WingTechCorner/I2C_Multiplexer/images/I2C-MuxBoard.png

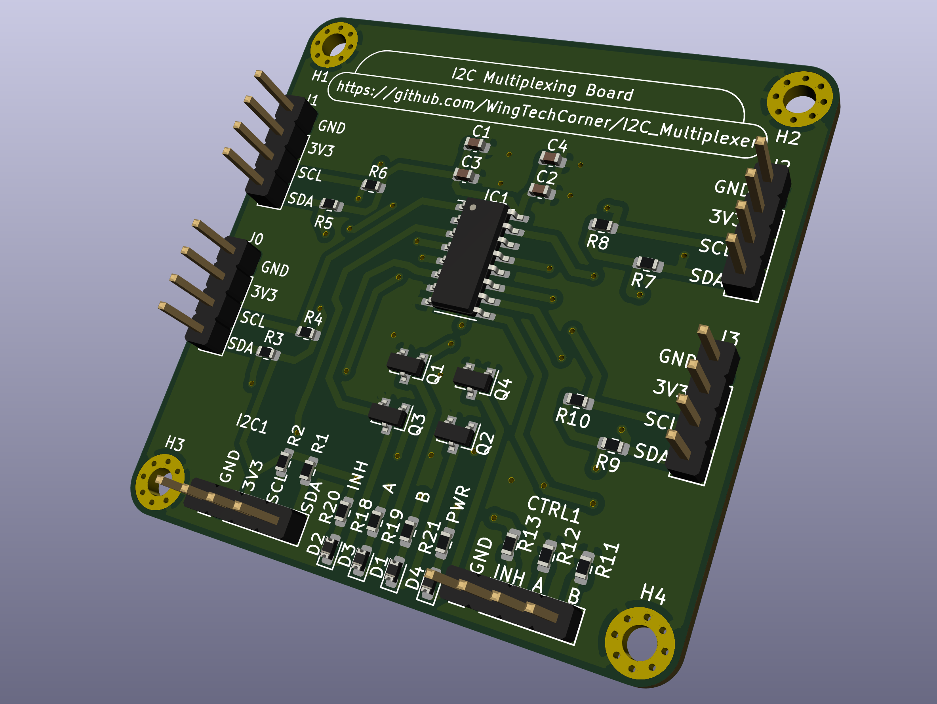
images/I2C-MuxBoard.png
